kb-elmo/sesame/acrylic_case/sheet-frame-bottom-usb.dxf

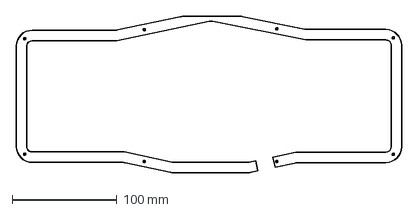
[picture p15: CAD file, 2021-01-16]
acrylic_case/sheet-frame-bottom-usb.dxf
368.4 x 149.6 mm
