kb-elmo/sesame/acrylic_case/sheet-frame-bottom.dxf

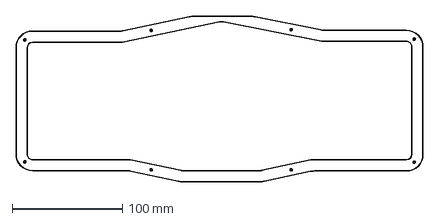
[picture p16: CAD file, 2021-01-16]
acrylic_case/sheet-frame-bottom.dxf
368.4 x 149.6 mm
