kb-elmo/sesame/acrylic_case/sheet-frame-top.dxf

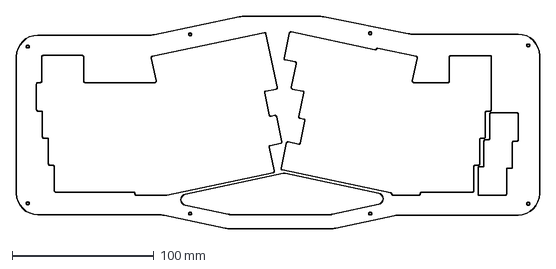
[picture p17: CAD file, 2021-01-16]
acrylic_case/sheet-frame-top.dxf
368.4 x 149.6 mm
