kb-elmo/sesame/acrylic_case/sheet-bottom.dxf

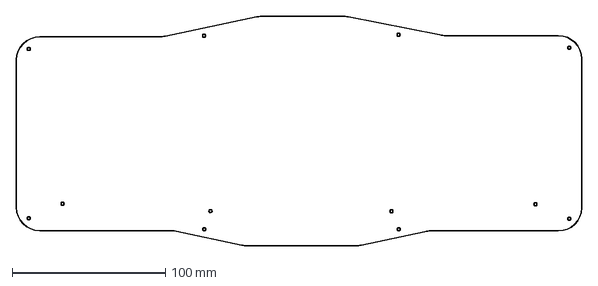
[picture p18: CAD file, 2021-01-16]
acrylic_case/sheet-bottom.dxf
368.4 x 149.6 mm
