kb-elmo/sesame/firmware/bootloader/updater/updater.asm

updater.elf:     file format elf32-avr

SYMBOL TABLE:
00000000 l    d  .text	00000000 .text
00800060 l    d  .data	00000000 .data
00000000 l    d  .comment	00000000 .comment
00000000 l    d  .note.gnu.avr.deviceinfo	00000000 .note.gnu.avr.deviceinfo
00000000 l    d  .debug_aranges	00000000 .debug_aranges
00000000 l    d  .debug_info	00000000 .debug_info
00000000 l    d  .debug_abbrev	00000000 .debug_abbrev
00000000 l    d  .debug_line	00000000 .debug_line
00000000 l    d  .debug_frame	00000000 .debug_frame
00000000 l    d  .debug_str	00000000 .debug_str
00000000 l    d  .debug_loc	00000000 .debug_loc
00000000 l    d  .debug_ranges	00000000 .debug_ranges
00000000 l    d  .debug_macro	00000000 .debug_macro
00000000 l    df *ABS*	00000000 updater.c
0000003e l       *ABS*	00000000 __SP_H__
0000003d l       *ABS*	00000000 __SP_L__
0000003f l       *ABS*	00000000 __SREG__
00000000 l       *ABS*	00000000 __tmp_reg__
00000001 l       *ABS*	00000000 __zero_reg__
0000009c l       .text	00000000 loop20
000000ca l       .text	00000000 loop48
00000000 l    df *ABS*	00000000 _exit.o
00000c1c l       .text	00000000 __stop_program
0000007a  w      .text	00000000 __vector_1
00800060 g     O .data	00000002 new_firmware
0000ffa0 g       *ABS*	00000000 __DATA_REGION_LENGTH__
0000007c g     F .text	0000002e do_spm
00000a62 g     F .text	00000012 memcpy_PF
00000054 g       .text	00000000 __trampolines_start
00000c1e g       .text	00000000 _etext
0000007a  w      .text	00000000 __vector_12
0000007a g       .text	00000000 __bad_interrupt
00000204 g       .text	00000000 usbasploader
00000c20 g       *ABS*	00000000 __data_load_end
0000007a  w      .text	00000000 __vector_6
00000054 g       .text	00000000 __trampolines_end
0000007a  w      .text	00000000 __vector_3
00000c1e g       *ABS*	00000000 __data_load_start
00000054 g       .text	00000000 __dtors_end
00000400 g       *ABS*	00000000 __LOCK_REGION_LENGTH__
0000007a  w      .text	00000000 __vector_11
00000054  w      .text	00000000 __init
00000a62 g       .text	00000000 _binary_usbasploader_raw_end
0000007a  w      .text	00000000 __vector_13
0000007a  w      .text	00000000 __vector_17
0000007a  w      .text	00000000 __vector_19
0000007a  w      .text	00000000 __vector_7
00810000 g       .data	00000000 __eeprom_end
00000000 g       .text	00000000 __vectors
00800062 g       .data	00000000 __data_end
0000085e g       *ABS*	00000000 _binary_usbasploader_raw_size
00000000  w      .text	00000000 __vector_default
0000007a  w      .text	00000000 __vector_5
000000fe g     F .text	00000106 mypgm_WRITEpage
000000d8 g     F .text	00000026 mypgm_readpage
00000400 g       *ABS*	00000000 __SIGNATURE_REGION_LENGTH__
00000054 g       .text	00000000 __ctors_start
00000060 g       .text	00000016 .hidden __do_copy_data
00000c0c g     F .text	0000000e memset
00000a74 g     F .text	00000198 main
0000007a  w      .text	00000000 __vector_4
00000000  w      *ABS*	00000000 __heap_end
0000007a  w      .text	00000000 __vector_9
0000007a  w      .text	00000000 __vector_2
00000400 g       *ABS*	00000000 __USER_SIGNATURE_REGION_LENGTH__
0000007a  w      .text	00000000 __vector_15
00000054 g       .text	00000000 __dtors_start
00000054 g       .text	00000000 __ctors_end
0000085f  w      *ABS*	00000000 __stack
00800062 g       .data	00000000 _edata
00800062 g       .data	00000000 _end
0000007a  w      .text	00000000 __vector_8
00000c1a  w      .text	00000000 .hidden exit
00010000 g       *ABS*	00000000 __EEPROM_REGION_LENGTH__
00000c1a g       .text	00000000 .hidden _exit
0000007a  w      .text	00000000 __vector_14
000000aa g     F .text	0000002e temp_do_spm
0000007a  w      .text	00000000 __vector_10
0000007a  w      .text	00000000 __vector_16
00800060 g       .data	00000000 __data_start
0000007a  w      .text	00000000 __vector_18
00000400 g       *ABS*	00000000 __FUSE_REGION_LENGTH__
00020000 g       *ABS*	00000000 __TEXT_REGION_LENGTH__
0000007a  w      .text	00000000 __vector_20



Disassembly of section .text:

00000000 <__vectors>:
   0:	29 c0       	rjmp	.+82     	; 0x54 <__ctors_end>
   2:	00 00       	nop
   4:	3a c0       	rjmp	.+116    	; 0x7a <__bad_interrupt>
   6:	00 00       	nop
   8:	38 c0       	rjmp	.+112    	; 0x7a <__bad_interrupt>
   a:	00 00       	nop
   c:	36 c0       	rjmp	.+108    	; 0x7a <__bad_interrupt>
   e:	00 00       	nop
  10:	34 c0       	rjmp	.+104    	; 0x7a <__bad_interrupt>
  12:	00 00       	nop
  14:	32 c0       	rjmp	.+100    	; 0x7a <__bad_interrupt>
  16:	00 00       	nop
  18:	30 c0       	rjmp	.+96     	; 0x7a <__bad_interrupt>
  1a:	00 00       	nop
  1c:	2e c0       	rjmp	.+92     	; 0x7a <__bad_interrupt>
  1e:	00 00       	nop
  20:	2c c0       	rjmp	.+88     	; 0x7a <__bad_interrupt>
  22:	00 00       	nop
  24:	2a c0       	rjmp	.+84     	; 0x7a <__bad_interrupt>
  26:	00 00       	nop
  28:	28 c0       	rjmp	.+80     	; 0x7a <__bad_interrupt>
  2a:	00 00       	nop
  2c:	26 c0       	rjmp	.+76     	; 0x7a <__bad_interrupt>
  2e:	00 00       	nop
  30:	24 c0       	rjmp	.+72     	; 0x7a <__bad_interrupt>
  32:	00 00       	nop
  34:	22 c0       	rjmp	.+68     	; 0x7a <__bad_interrupt>
  36:	00 00       	nop
  38:	20 c0       	rjmp	.+64     	; 0x7a <__bad_interrupt>
  3a:	00 00       	nop
  3c:	1e c0       	rjmp	.+60     	; 0x7a <__bad_interrupt>
  3e:	00 00       	nop
  40:	1c c0       	rjmp	.+56     	; 0x7a <__bad_interrupt>
  42:	00 00       	nop
  44:	1a c0       	rjmp	.+52     	; 0x7a <__bad_interrupt>
  46:	00 00       	nop
  48:	18 c0       	rjmp	.+48     	; 0x7a <__bad_interrupt>
  4a:	00 00       	nop
  4c:	16 c0       	rjmp	.+44     	; 0x7a <__bad_interrupt>
  4e:	00 00       	nop
  50:	14 c0       	rjmp	.+40     	; 0x7a <__bad_interrupt>
	...

00000054 <__ctors_end>:
  54:	11 24       	eor	r1, r1
  56:	1f be       	out	0x3f, r1	; 63
  58:	cf e5       	ldi	r28, 0x5F	; 95
  5a:	d8 e0       	ldi	r29, 0x08	; 8
  5c:	de bf       	out	0x3e, r29	; 62
  5e:	cd bf       	out	0x3d, r28	; 61

00000060 <__do_copy_data>:
  60:	10 e0       	ldi	r17, 0x00	; 0
  62:	a0 e6       	ldi	r26, 0x60	; 96
  64:	b0 e0       	ldi	r27, 0x00	; 0
  66:	ee e1       	ldi	r30, 0x1E	; 30
  68:	fc e0       	ldi	r31, 0x0C	; 12
  6a:	02 c0       	rjmp	.+4      	; 0x70 <__do_copy_data+0x10>
  6c:	05 90       	lpm	r0, Z+
  6e:	0d 92       	st	X+, r0
  70:	a2 36       	cpi	r26, 0x62	; 98
  72:	b1 07       	cpc	r27, r17
  74:	d9 f7       	brne	.-10     	; 0x6c <__do_copy_data+0xc>
  76:	fe d4       	rcall	.+2556   	; 0xa74 <main>
  78:	d0 c5       	rjmp	.+2976   	; 0xc1a <_exit>

0000007a <__bad_interrupt>:
  7a:	c2 cf       	rjmp	.-124    	; 0x0 <__vectors>

0000007c <do_spm>:
      );												\
  })
#endif

#if (!(defined(BOOTLOADER_ADDRESS))) || (defined(NEW_BOOTLOADER_ADDRESS))
void do_spm(const uint32_t flash_byteaddress, const uint8_t spmcrval, const uint16_t dataword) {
  7c:	bf 92       	push	r11
  7e:	cf 92       	push	r12
  80:	df 92       	push	r13
  82:	d9 01       	movw	r26, r18
    __do_spm_Ex(flash_byteaddress, spmcrval, dataword, funcaddr___bootloader__do_spm >> 1);
  84:	ea e2       	ldi	r30, 0x2A	; 42
  86:	f8 e3       	ldi	r31, 0x38	; 56
  88:	0f 92       	push	r0
  8a:	1f 92       	push	r1
  8c:	d7 2e       	mov	r13, r23
  8e:	c6 2e       	mov	r12, r22
  90:	b8 2e       	mov	r11, r24
  92:	24 2f       	mov	r18, r20
  94:	1b 2e       	mov	r1, r27
  96:	0a 2e       	mov	r0, r26
  98:	09 95       	icall
  9a:	21 31       	cpi	r18, 0x11	; 17

0000009c <loop20>:
  9c:	f9 f7       	brne	.-2      	; 0x9c <loop20>
  9e:	1f 90       	pop	r1
  a0:	0f 90       	pop	r0
}
  a2:	df 90       	pop	r13
  a4:	cf 90       	pop	r12
  a6:	bf 90       	pop	r11
  a8:	08 95       	ret

000000aa <temp_do_spm>:
void new_do_spm(const uint32_t flash_byteaddress, const uint8_t spmcrval, const uint16_t dataword) {
    __do_spm_Ex(flash_byteaddress, spmcrval, dataword, NEW_SPM_ADDRESS >> 1);
}
#endif

void temp_do_spm(const uint32_t flash_byteaddress, const uint8_t spmcrval, const uint16_t dataword) {
  aa:	bf 92       	push	r11
  ac:	cf 92       	push	r12
  ae:	df 92       	push	r13
  b0:	d9 01       	movw	r26, r18
    __do_spm_Ex(flash_byteaddress, spmcrval, dataword, TEMP_SPM_ADDRESS >> 1);
  b2:	ea e2       	ldi	r30, 0x2A	; 42
  b4:	ff e3       	ldi	r31, 0x3F	; 63
  b6:	0f 92       	push	r0
  b8:	1f 92       	push	r1
  ba:	d7 2e       	mov	r13, r23
  bc:	c6 2e       	mov	r12, r22
  be:	b8 2e       	mov	r11, r24
  c0:	24 2f       	mov	r18, r20
  c2:	1b 2e       	mov	r1, r27
  c4:	0a 2e       	mov	r0, r26
  c6:	09 95       	icall
  c8:	21 31       	cpi	r18, 0x11	; 17

000000ca <loop48>:
  ca:	f9 f7       	brne	.-2      	; 0xca <loop48>
  cc:	1f 90       	pop	r1
  ce:	0f 90       	pop	r0
}
  d0:	df 90       	pop	r13
  d2:	cf 90       	pop	r12
  d4:	bf 90       	pop	r11
  d6:	08 95       	ret

000000d8 <mypgm_readpage>:
  
  return result;
}
#else
// replace it somehow with "memcpy_PF" in order to save some ops...
size_t mypgm_readpage(const mypgm_addr_t byteaddress,const void* buffer, const size_t bufferbytesize) {
  d8:	cf 93       	push	r28
  da:	df 93       	push	r29
  dc:	fa 01       	movw	r30, r20
  de:	e9 01       	movw	r28, r18
  size_t	result		= (bufferbytesize < SPM_PAGESIZE)?bufferbytesize:SPM_PAGESIZE;
  e0:	21 38       	cpi	r18, 0x81	; 129
  e2:	31 05       	cpc	r19, r1
  e4:	10 f0       	brcs	.+4      	; 0xea <mypgm_readpage+0x12>
  e6:	c0 e8       	ldi	r28, 0x80	; 128
  e8:	d0 e0       	ldi	r29, 0x00	; 0
  mypgm_addr_t	pageaddr	= byteaddress - (byteaddress % SPM_PAGESIZE);
  ea:	ab 01       	movw	r20, r22
  ec:	bc 01       	movw	r22, r24
  ee:	40 78       	andi	r20, 0x80	; 128
  
  mymemcpy_PF((void*)buffer, (uint_farptr_t)pageaddr, result);
  f0:	9e 01       	movw	r18, r28
  f2:	cf 01       	movw	r24, r30
  f4:	b6 d4       	rcall	.+2412   	; 0xa62 <memcpy_PF>
  
  return result;
}
  f6:	ce 01       	movw	r24, r28
  f8:	df 91       	pop	r29
  fa:	cf 91       	pop	r28
  fc:	08 95       	ret

000000fe <mypgm_WRITEpage>:
#endif

#ifdef CONFIG_UPDATER_REDUCEWRITES
size_t mypgm_WRITEpage(const mypgm_addr_t byteaddress,const void* buffer, const size_t bufferbytesize, mypgm_spminterface spmfunc) {
  fe:	2f 92       	push	r2
 100:	3f 92       	push	r3
 102:	4f 92       	push	r4
 104:	5f 92       	push	r5
 106:	6f 92       	push	r6
 108:	7f 92       	push	r7
 10a:	8f 92       	push	r8
 10c:	9f 92       	push	r9
 10e:	af 92       	push	r10
 110:	bf 92       	push	r11
 112:	cf 92       	push	r12
 114:	df 92       	push	r13
 116:	ef 92       	push	r14
 118:	ff 92       	push	r15
 11a:	0f 93       	push	r16
 11c:	1f 93       	push	r17
 11e:	cf 93       	push	r28
 120:	df 93       	push	r29
 122:	48 01       	movw	r8, r16
  size_t	result		= (bufferbytesize < SPM_PAGESIZE)?bufferbytesize:SPM_PAGESIZE;
 124:	e9 01       	movw	r28, r18
 126:	21 38       	cpi	r18, 0x81	; 129
 128:	31 05       	cpc	r19, r1
 12a:	10 f0       	brcs	.+4      	; 0x130 <mypgm_WRITEpage+0x32>
 12c:	c0 e8       	ldi	r28, 0x80	; 128
 12e:	d0 e0       	ldi	r29, 0x00	; 0
  size_t	pagesize	= result >> 1;
 130:	1e 01       	movw	r2, r28
 132:	36 94       	lsr	r3
 134:	27 94       	ror	r2
  uint16_t	*pagedata	= (void*)buffer;
  mypgm_addr_t	pageaddr_bakup	= byteaddress - (byteaddress % SPM_PAGESIZE);
 136:	6b 01       	movw	r12, r22
 138:	7c 01       	movw	r14, r24
 13a:	20 e8       	ldi	r18, 0x80	; 128
 13c:	c2 22       	and	r12, r18
  uint8_t	changed=0, needs_erase=0;
  uint16_t	deeword;
  size_t	i;
  
  // just check, if page needs a rewrite or an erase...
  for (i=0;i<pagesize;i+=1) {
 13e:	8a 01       	movw	r16, r20
 140:	da 01       	movw	r26, r20
 142:	90 e0       	ldi	r25, 0x00	; 0
 144:	80 e0       	ldi	r24, 0x00	; 0
  uint8_t	changed=0, needs_erase=0;
 146:	60 e0       	ldi	r22, 0x00	; 0
 148:	70 e0       	ldi	r23, 0x00	; 0
  for (i=0;i<pagesize;i+=1) {
 14a:	82 15       	cp	r24, r2
 14c:	93 05       	cpc	r25, r3
 14e:	71 f5       	brne	.+92     	; 0x1ac <mypgm_WRITEpage+0xae>
    if ((~deeword) != 0) needs_erase=1;
      
    pageaddr+=2;
  }

  if (changed) {
 150:	77 23       	and	r23, r23
 152:	09 f4       	brne	.+2      	; 0x156 <mypgm_WRITEpage+0x58>
 154:	54 c0       	rjmp	.+168    	; 0x1fe <mypgm_WRITEpage+0x100>
    
    if (needs_erase) {
 156:	66 23       	and	r22, r22
 158:	39 f0       	breq	.+14     	; 0x168 <mypgm_WRITEpage+0x6a>
      //do a page-erase, ATTANTION: flash only can be erased a limited number of times !
      spmfunc(pageaddr_bakup, updater_pageerasecode, 0);
 15a:	30 e0       	ldi	r19, 0x00	; 0
 15c:	20 e0       	ldi	r18, 0x00	; 0
 15e:	43 e0       	ldi	r20, 0x03	; 3
 160:	c7 01       	movw	r24, r14
 162:	b6 01       	movw	r22, r12
 164:	f4 01       	movw	r30, r8
 166:	09 95       	icall
  uint8_t	changed=0, needs_erase=0;
 168:	26 01       	movw	r4, r12
 16a:	37 01       	movw	r6, r14
 16c:	b1 2c       	mov	r11, r1
 16e:	a1 2c       	mov	r10, r1
    
    // from now on, the page is assumed empty !! (hopefully our code is located somewhere else!)
    // now, fill the tempoary buffer
    // ATTANTION: see comment on "do_spm" !
    pageaddr	= pageaddr_bakup;
    for (i=0;i<pagesize;i+=1) {
 170:	a2 14       	cp	r10, r2
 172:	b3 04       	cpc	r11, r3
 174:	91 f5       	brne	.+100    	; 0x1da <mypgm_WRITEpage+0xdc>
      spmfunc(pageaddr, updater_pagefillcode, pagedata[i]);
      pageaddr+=2;
    }
    
    // so, now finally write the page to the FLASH
    spmfunc(pageaddr_bakup, updater_pagewritecode, 0);
 176:	30 e0       	ldi	r19, 0x00	; 0
 178:	20 e0       	ldi	r18, 0x00	; 0
 17a:	45 e0       	ldi	r20, 0x05	; 5
 17c:	c7 01       	movw	r24, r14
 17e:	b6 01       	movw	r22, r12
 180:	f4 01       	movw	r30, r8
 182:	09 95       	icall
    result = 0;
  }
  
  
  return result;
}
 184:	ce 01       	movw	r24, r28
 186:	df 91       	pop	r29
 188:	cf 91       	pop	r28
 18a:	1f 91       	pop	r17
 18c:	0f 91       	pop	r16
 18e:	ff 90       	pop	r15
 190:	ef 90       	pop	r14
 192:	df 90       	pop	r13
 194:	cf 90       	pop	r12
 196:	bf 90       	pop	r11
 198:	af 90       	pop	r10
 19a:	9f 90       	pop	r9
 19c:	8f 90       	pop	r8
 19e:	7f 90       	pop	r7
 1a0:	6f 90       	pop	r6
 1a2:	5f 90       	pop	r5
 1a4:	4f 90       	pop	r4
 1a6:	3f 90       	pop	r3
 1a8:	2f 90       	pop	r2
 1aa:	08 95       	ret
    deeword=pgm_read_word(pageaddr);
 1ac:	fc 01       	movw	r30, r24
 1ae:	ee 0f       	add	r30, r30
 1b0:	ff 1f       	adc	r31, r31
 1b2:	ec 0d       	add	r30, r12
 1b4:	fd 1d       	adc	r31, r13
 1b6:	25 91       	lpm	r18, Z+
 1b8:	34 91       	lpm	r19, Z
    if (deeword != pagedata[i]) changed=1;
 1ba:	4d 91       	ld	r20, X+
 1bc:	5d 91       	ld	r21, X+
 1be:	42 17       	cp	r20, r18
 1c0:	53 07       	cpc	r21, r19
 1c2:	49 f0       	breq	.+18     	; 0x1d6 <mypgm_WRITEpage+0xd8>
    deeword |= ~pagedata[i];
 1c4:	40 95       	com	r20
 1c6:	50 95       	com	r21
 1c8:	24 2b       	or	r18, r20
 1ca:	35 2b       	or	r19, r21
    if (deeword != pagedata[i]) changed=1;
 1cc:	71 e0       	ldi	r23, 0x01	; 1
    if ((~deeword) != 0) needs_erase=1;
 1ce:	2f 3f       	cpi	r18, 0xFF	; 255
 1d0:	3f 4f       	sbci	r19, 0xFF	; 255
 1d2:	09 f0       	breq	.+2      	; 0x1d6 <mypgm_WRITEpage+0xd8>
 1d4:	61 e0       	ldi	r22, 0x01	; 1
  for (i=0;i<pagesize;i+=1) {
 1d6:	01 96       	adiw	r24, 0x01	; 1
 1d8:	b8 cf       	rjmp	.-144    	; 0x14a <mypgm_WRITEpage+0x4c>
      spmfunc(pageaddr, updater_pagefillcode, pagedata[i]);
 1da:	f8 01       	movw	r30, r16
 1dc:	21 91       	ld	r18, Z+
 1de:	31 91       	ld	r19, Z+
 1e0:	8f 01       	movw	r16, r30
 1e2:	41 e0       	ldi	r20, 0x01	; 1
 1e4:	c3 01       	movw	r24, r6
 1e6:	b2 01       	movw	r22, r4
 1e8:	f4 01       	movw	r30, r8
 1ea:	09 95       	icall
      pageaddr+=2;
 1ec:	f2 e0       	ldi	r31, 0x02	; 2
 1ee:	4f 0e       	add	r4, r31
 1f0:	51 1c       	adc	r5, r1
 1f2:	61 1c       	adc	r6, r1
 1f4:	71 1c       	adc	r7, r1
    for (i=0;i<pagesize;i+=1) {
 1f6:	2f ef       	ldi	r18, 0xFF	; 255
 1f8:	a2 1a       	sub	r10, r18
 1fa:	b2 0a       	sbc	r11, r18
 1fc:	b9 cf       	rjmp	.-142    	; 0x170 <mypgm_WRITEpage+0x72>
    result = 0;
 1fe:	d0 e0       	ldi	r29, 0x00	; 0
 200:	c0 e0       	ldi	r28, 0x00	; 0
  return result;
 202:	c0 cf       	rjmp	.-128    	; 0x184 <mypgm_WRITEpage+0x86>

00000204 <usbasploader>:
 204:	61 c0       	rjmp	.+194    	; 0x2c8 <usbasploader+0xc4>
 206:	00 00       	nop
 208:	a0 c0       	rjmp	.+320    	; 0x34a <usbasploader+0x146>
 20a:	00 00       	nop
 20c:	84 c0       	rjmp	.+264    	; 0x316 <usbasploader+0x112>
 20e:	00 00       	nop
 210:	82 c0       	rjmp	.+260    	; 0x316 <usbasploader+0x112>
 212:	00 00       	nop
 214:	80 c0       	rjmp	.+256    	; 0x316 <usbasploader+0x112>
 216:	00 00       	nop
 218:	7e c0       	rjmp	.+252    	; 0x316 <usbasploader+0x112>
 21a:	00 00       	nop
 21c:	7c c0       	rjmp	.+248    	; 0x316 <usbasploader+0x112>
 21e:	00 00       	nop
 220:	7a c0       	rjmp	.+244    	; 0x316 <usbasploader+0x112>
 222:	00 00       	nop
 224:	78 c0       	rjmp	.+240    	; 0x316 <usbasploader+0x112>
 226:	00 00       	nop
 228:	76 c0       	rjmp	.+236    	; 0x316 <usbasploader+0x112>
 22a:	00 00       	nop
 22c:	74 c0       	rjmp	.+232    	; 0x316 <usbasploader+0x112>
 22e:	00 00       	nop
 230:	72 c0       	rjmp	.+228    	; 0x316 <usbasploader+0x112>
 232:	00 00       	nop
 234:	70 c0       	rjmp	.+224    	; 0x316 <usbasploader+0x112>
 236:	00 00       	nop
 238:	6e c0       	rjmp	.+220    	; 0x316 <usbasploader+0x112>
 23a:	00 00       	nop
 23c:	6c c0       	rjmp	.+216    	; 0x316 <usbasploader+0x112>
 23e:	00 00       	nop
 240:	6a c0       	rjmp	.+212    	; 0x316 <usbasploader+0x112>
 242:	00 00       	nop
 244:	68 c0       	rjmp	.+208    	; 0x316 <usbasploader+0x112>
 246:	00 00       	nop
 248:	66 c0       	rjmp	.+204    	; 0x316 <usbasploader+0x112>
 24a:	00 00       	nop
 24c:	64 c0       	rjmp	.+200    	; 0x316 <usbasploader+0x112>
 24e:	00 00       	nop
 250:	62 c0       	rjmp	.+196    	; 0x316 <usbasploader+0x112>
 252:	00 00       	nop
 254:	60 c0       	rjmp	.+192    	; 0x316 <usbasploader+0x112>
 256:	00 00       	nop
 258:	ec 2d       	mov	r30, r12
 25a:	fd 2d       	mov	r31, r13
 25c:	b7 b6       	in	r11, 0x37	; 55
 25e:	b0 fc       	sbrc	r11, 0
 260:	fd cf       	rjmp	.-6      	; 0x25c <usbasploader+0x58>
 262:	27 bf       	out	0x37, r18	; 55
 264:	e8 95       	spm
 266:	b7 b6       	in	r11, 0x37	; 55
 268:	b0 fc       	sbrc	r11, 0
 26a:	fd cf       	rjmp	.-6      	; 0x266 <usbasploader+0x62>
 26c:	21 e1       	ldi	r18, 0x11	; 17
 26e:	b7 b6       	in	r11, 0x37	; 55
 270:	b6 fc       	sbrc	r11, 6
 272:	f4 cf       	rjmp	.-24     	; 0x25c <usbasploader+0x58>
 274:	08 95       	ret
 276:	09 02       	muls	r16, r25
 278:	12 00       	.word	0x0012	; ????
 27a:	01 01       	movw	r0, r2
 27c:	00 80       	ld	r0, Z
 27e:	32 09       	sbc	r19, r2
 280:	04 00       	.word	0x0004	; ????
 282:	00 00       	nop
 284:	00 00       	nop
 286:	00 00       	nop
 288:	12 01       	movw	r2, r4
 28a:	10 01       	movw	r2, r0
 28c:	ff 00       	.word	0x00ff	; ????
 28e:	00 08       	sbc	r0, r0
 290:	c0 16       	cp	r12, r16
 292:	dc 05       	cpc	r29, r12
 294:	02 01       	movw	r0, r4
 296:	01 02       	muls	r16, r17
 298:	00 01       	movw	r0, r0
 29a:	0e 03       	fmul	r16, r22
 29c:	55 00       	.word	0x0055	; ????
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
 a52:	0f be       	out	0x3f, r0	; 63
 a54:	01 96       	adiw	r24, 0x01	; 1
 a56:	08 95       	ret
 a58:	f8 94       	cli
 a5a:	ff cf       	rjmp	.-2      	; 0xa5a <__stack+0x1fb>
 a5c:	ff 5a       	subi	r31, 0xAF	; 175
 a5e:	1e 95 02 00 	call	0x440004	; 0x440004 <__TEXT_REGION_LENGTH__+0x420004>

00000a62 <memcpy_PF>:
 a62:	fa 01       	movw	r30, r20
 a64:	dc 01       	movw	r26, r24
 a66:	02 c0       	rjmp	.+4      	; 0xa6c <memcpy_PF+0xa>
 a68:	05 90       	lpm	r0, Z+
 a6a:	0d 92       	st	X+, r0
 a6c:	21 50       	subi	r18, 0x01	; 1
 a6e:	30 40       	sbci	r19, 0x00	; 0
 a70:	d8 f7       	brcc	.-10     	; 0xa68 <memcpy_PF+0x6>
 a72:	08 95       	ret

00000a74 <main>:
#include "crccheck.c"
#endif

// #pragma GCC diagnostic ignored "-Wno-pointer-to-int-cast"
int main(void)
{
 a74:	cd b7       	in	r28, 0x3d	; 61
 a76:	de b7       	in	r29, 0x3e	; 62
 a78:	c0 58       	subi	r28, 0x80	; 128
 a7a:	d1 09       	sbc	r29, r1
 a7c:	0f b6       	in	r0, 0x3f	; 63
 a7e:	f8 94       	cli
 a80:	de bf       	out	0x3e, r29	; 62
 a82:	0f be       	out	0x3f, r0	; 63
 a84:	cd bf       	out	0x3d, r28	; 61
    uint32_t crcval;
#endif
    size_t  i;
    uint8_t buffer[SPM_PAGESIZE];
    
    MCUCSR = 0; /* do not care about previous reset - just disable the wdt */
 a86:	14 be       	out	0x34, r1	; 52
void wdt_disable (void)
{
	if (_SFR_IO_REG_P (_WD_CONTROL_REG))
	{
        uint8_t register temp_reg;
		__asm__ __volatile__ (
 a88:	0f b6       	in	r0, 0x3f	; 63
 a8a:	f8 94       	cli
 a8c:	a8 95       	wdr
 a8e:	81 b5       	in	r24, 0x21	; 33
 a90:	88 61       	ori	r24, 0x18	; 24
 a92:	81 bd       	out	0x21, r24	; 33
 a94:	11 bc       	out	0x21, r1	; 33
 a96:	0f be       	out	0x3f, r0	; 63
    wdt_disable();
    cli();
 a98:	f8 94       	cli
    if (crcval == ((uint32_t)UPDATECRC32)) {
#endif

    // check if firmware would change...
    buffer[0]=0;
    for (i=0;i<SIZEOF_new_firmware;i+=2) {
 a9a:	20 91 60 00 	lds	r18, 0x0060	; 0x800060 <new_firmware>
 a9e:	30 91 61 00 	lds	r19, 0x0061	; 0x800061 <new_firmware+0x1>
      uint16_t a, b;
#if (FLASHEND > 65535)
      a=pgm_read_word_far(FULLCORRECTFLASHADDRESS(&new_firmware[i]));
      b=pgm_read_word_far(NEW_BOOTLOADER_ADDRESS+i);
#else
      a=pgm_read_word(FULLCORRECTFLASHADDRESS(&new_firmware[i]));
 aa2:	80 e0       	ldi	r24, 0x00	; 0
 aa4:	90 e7       	ldi	r25, 0x70	; 112
 aa6:	f9 01       	movw	r30, r18
 aa8:	65 91       	lpm	r22, Z+
 aaa:	74 91       	lpm	r23, Z
      b=pgm_read_word(NEW_BOOTLOADER_ADDRESS+i);
 aac:	fc 01       	movw	r30, r24
 aae:	45 91       	lpm	r20, Z+
 ab0:	54 91       	lpm	r21, Z
#endif
      if (a!=b) {
 ab2:	64 17       	cp	r22, r20
 ab4:	75 07       	cpc	r23, r21
 ab6:	09 f4       	brne	.+2      	; 0xaba <main+0x46>
 ab8:	94 c0       	rjmp	.+296    	; 0xbe2 <main+0x16e>
	buffer[0]=1;
 aba:	81 e0       	ldi	r24, 0x01	; 1
 abc:	89 83       	std	Y+1, r24	; 0x01
 abe:	94 e5       	ldi	r25, 0x54	; 84
 ac0:	c9 2e       	mov	r12, r25
 ac2:	90 e7       	ldi	r25, 0x70	; 112
 ac4:	d9 2e       	mov	r13, r25
 ac6:	e1 2c       	mov	r14, r1
 ac8:	f1 2c       	mov	r15, r1
  mypgm_addr_t	pageaddr	= byteaddress - (byteaddress % SPM_PAGESIZE);
 aca:	b7 01       	movw	r22, r14
 acc:	a6 01       	movw	r20, r12
 ace:	40 78       	andi	r20, 0x80	; 128
  mymemcpy_PF((void*)buffer, (uint_farptr_t)pageaddr, result);
 ad0:	20 e8       	ldi	r18, 0x80	; 128
 ad2:	30 e0       	ldi	r19, 0x00	; 0
 ad4:	ce 01       	movw	r24, r28
 ad6:	01 96       	adiw	r24, 0x01	; 1
 ad8:	c4 df       	rcall	.-120    	; 0xa62 <memcpy_PF>
    if (buffer[0]) {

      // A
      // copy the current "bootloader__do_spm" to tempoary position via std. "bootloader__do_spm"
      for (i=0;i<TEMP_SPM_BLKSIZE;i+=SPM_PAGESIZE) {
	mypgm_WRITEpage(TEMP_SPM_PAGEADR+i, buffer, mypgm_readpage(funcaddr___bootloader__do_spm+i, buffer, sizeof(buffer)), do_spm);
 ada:	c7 01       	movw	r24, r14
 adc:	b6 01       	movw	r22, r12
 ade:	64 55       	subi	r22, 0x54	; 84
 ae0:	72 4f       	sbci	r23, 0xF2	; 242
 ae2:	8f 4f       	sbci	r24, 0xFF	; 255
 ae4:	9f 4f       	sbci	r25, 0xFF	; 255
 ae6:	0e e3       	ldi	r16, 0x3E	; 62
 ae8:	10 e0       	ldi	r17, 0x00	; 0
 aea:	20 e8       	ldi	r18, 0x80	; 128
 aec:	30 e0       	ldi	r19, 0x00	; 0
 aee:	ae 01       	movw	r20, r28
 af0:	4f 5f       	subi	r20, 0xFF	; 255
 af2:	5f 4f       	sbci	r21, 0xFF	; 255
 af4:	04 db       	rcall	.-2552   	; 0xfe <mypgm_WRITEpage>
 af6:	80 e8       	ldi	r24, 0x80	; 128
 af8:	c8 0e       	add	r12, r24
 afa:	d1 1c       	adc	r13, r1
 afc:	e1 1c       	adc	r14, r1
 afe:	f1 1c       	adc	r15, r1
      for (i=0;i<TEMP_SPM_BLKSIZE;i+=SPM_PAGESIZE) {
 b00:	24 e5       	ldi	r18, 0x54	; 84
 b02:	c2 16       	cp	r12, r18
 b04:	22 e7       	ldi	r18, 0x72	; 114
 b06:	d2 06       	cpc	r13, r18
 b08:	e1 04       	cpc	r14, r1
 b0a:	f1 04       	cpc	r15, r1
 b0c:	f1 f6       	brne	.-68     	; 0xaca <main+0x56>
 b0e:	c1 2c       	mov	r12, r1
 b10:	80 e7       	ldi	r24, 0x70	; 112
 b12:	d8 2e       	mov	r13, r24
 b14:	e1 2c       	mov	r14, r1
 b16:	f1 2c       	mov	r15, r1
 b18:	56 01       	movw	r10, r12
 b1a:	40 e7       	ldi	r20, 0x70	; 112
 b1c:	b4 1a       	sub	r11, r20
      // B
      // start updating the firmware to "NEW_BOOTLOADER_ADDRESS" until at least "TEMP_SPM_BLKSIZE"-bytes after "NEW_SPM_ADDRESS" were written
      // therefore use the tempoary "bootloader__do_spm" (since we most probably will overwrite the default do_spm)
      for (i=0;;i+=SPM_PAGESIZE) {
#ifdef CONFIG_UPDATER_CLEANMEMCLEAR
	memset((void*)buffer, 0xff, sizeof(buffer));
 b1e:	40 e8       	ldi	r20, 0x80	; 128
 b20:	50 e0       	ldi	r21, 0x00	; 0
 b22:	6f ef       	ldi	r22, 0xFF	; 255
 b24:	70 e0       	ldi	r23, 0x00	; 0
 b26:	ce 01       	movw	r24, r28
 b28:	01 96       	adiw	r24, 0x01	; 1
 b2a:	70 d0       	rcall	.+224    	; 0xc0c <memset>
#endif
	mymemcpy_PF((void*)buffer, (uint_farptr_t)(FULLCORRECTFLASHADDRESS(&new_firmware[i])), ((SIZEOF_new_firmware-i)>sizeof(buffer))?sizeof(buffer):(SIZEOF_new_firmware-i));
 b2c:	40 91 60 00 	lds	r20, 0x0060	; 0x800060 <new_firmware>
 b30:	50 91 61 00 	lds	r21, 0x0061	; 0x800061 <new_firmware+0x1>
 b34:	4a 0d       	add	r20, r10
 b36:	5b 1d       	adc	r21, r11
 b38:	05 2e       	mov	r0, r21
 b3a:	00 0c       	add	r0, r0
 b3c:	66 0b       	sbc	r22, r22
 b3e:	77 0b       	sbc	r23, r23
 b40:	20 e8       	ldi	r18, 0x80	; 128
 b42:	30 e0       	ldi	r19, 0x00	; 0
 b44:	ce 01       	movw	r24, r28
 b46:	01 96       	adiw	r24, 0x01	; 1
 b48:	8c df       	rcall	.-232    	; 0xa62 <memcpy_PF>
	
	mypgm_WRITEpage(NEW_BOOTLOADER_ADDRESS+i, buffer, sizeof(buffer), temp_do_spm);
 b4a:	05 e5       	ldi	r16, 0x55	; 85
 b4c:	10 e0       	ldi	r17, 0x00	; 0
 b4e:	20 e8       	ldi	r18, 0x80	; 128
 b50:	30 e0       	ldi	r19, 0x00	; 0
 b52:	ae 01       	movw	r20, r28
 b54:	4f 5f       	subi	r20, 0xFF	; 255
 b56:	5f 4f       	sbci	r21, 0xFF	; 255
 b58:	c7 01       	movw	r24, r14
 b5a:	b6 01       	movw	r22, r12
 b5c:	d0 da       	rcall	.-2656   	; 0xfe <mypgm_WRITEpage>
	
	if ((NEW_BOOTLOADER_ADDRESS+i) > (NEW_SPM_ADDRESS+TEMP_SPM_BLKSIZE)) break;
 b5e:	d7 01       	movw	r26, r14
 b60:	c6 01       	movw	r24, r12
 b62:	80 58       	subi	r24, 0x80	; 128
 b64:	9f 4f       	sbci	r25, 0xFF	; 255
 b66:	af 4f       	sbci	r26, 0xFF	; 255
 b68:	bf 4f       	sbci	r27, 0xFF	; 255
 b6a:	81 15       	cp	r24, r1
 b6c:	23 e7       	ldi	r18, 0x73	; 115
 b6e:	92 07       	cpc	r25, r18
 b70:	a1 05       	cpc	r26, r1
 b72:	b1 05       	cpc	r27, r1
 b74:	09 f0       	breq	.+2      	; 0xb78 <main+0x104>
 b76:	47 c0       	rjmp	.+142    	; 0xc06 <main+0x192>

      // C
      // continue writeing the new_firmware after "NEW_SPM_ADDRESS+TEMP_SPM_BLKSIZE" this time use the "new_do_spm"
      for (;i<SIZEOF_new_firmware;i+=SPM_PAGESIZE) {
#ifdef CONFIG_UPDATER_CLEANMEMCLEAR
	memset((void*)buffer, 0xff, sizeof(buffer));
 b78:	40 e8       	ldi	r20, 0x80	; 128
 b7a:	50 e0       	ldi	r21, 0x00	; 0
 b7c:	6f ef       	ldi	r22, 0xFF	; 255
 b7e:	70 e0       	ldi	r23, 0x00	; 0
 b80:	ce 01       	movw	r24, r28
 b82:	01 96       	adiw	r24, 0x01	; 1
 b84:	43 d0       	rcall	.+134    	; 0xc0c <memset>
#endif
	mymemcpy_PF((void*)buffer, (uint_farptr_t)(FULLCORRECTFLASHADDRESS(&new_firmware[i])), ((SIZEOF_new_firmware-i)>sizeof(buffer))?sizeof(buffer):(SIZEOF_new_firmware-i));
 b86:	2e e5       	ldi	r18, 0x5E	; 94
 b88:	38 e0       	ldi	r19, 0x08	; 8
 b8a:	2a 19       	sub	r18, r10
 b8c:	3b 09       	sbc	r19, r11
 b8e:	21 38       	cpi	r18, 0x81	; 129
 b90:	31 05       	cpc	r19, r1
 b92:	10 f0       	brcs	.+4      	; 0xb98 <main+0x124>
 b94:	20 e8       	ldi	r18, 0x80	; 128
 b96:	30 e0       	ldi	r19, 0x00	; 0
 b98:	40 91 60 00 	lds	r20, 0x0060	; 0x800060 <new_firmware>
 b9c:	50 91 61 00 	lds	r21, 0x0061	; 0x800061 <new_firmware+0x1>
 ba0:	4a 0d       	add	r20, r10
 ba2:	5b 1d       	adc	r21, r11
 ba4:	05 2e       	mov	r0, r21
 ba6:	00 0c       	add	r0, r0
 ba8:	66 0b       	sbc	r22, r22
 baa:	77 0b       	sbc	r23, r23
 bac:	ce 01       	movw	r24, r28
 bae:	01 96       	adiw	r24, 0x01	; 1
 bb0:	58 df       	rcall	.-336    	; 0xa62 <memcpy_PF>

	mypgm_WRITEpage(NEW_BOOTLOADER_ADDRESS+i, buffer, sizeof(buffer), new_do_spm);
 bb2:	0e e3       	ldi	r16, 0x3E	; 62
 bb4:	10 e0       	ldi	r17, 0x00	; 0
 bb6:	20 e8       	ldi	r18, 0x80	; 128
 bb8:	30 e0       	ldi	r19, 0x00	; 0
 bba:	ae 01       	movw	r20, r28
 bbc:	4f 5f       	subi	r20, 0xFF	; 255
 bbe:	5f 4f       	sbci	r21, 0xFF	; 255
 bc0:	c7 01       	movw	r24, r14
 bc2:	b6 01       	movw	r22, r12
 bc4:	9c da       	rcall	.-2760   	; 0xfe <mypgm_WRITEpage>
      for (;i<SIZEOF_new_firmware;i+=SPM_PAGESIZE) {
 bc6:	40 e8       	ldi	r20, 0x80	; 128
 bc8:	a4 0e       	add	r10, r20
 bca:	b1 1c       	adc	r11, r1
 bcc:	80 e8       	ldi	r24, 0x80	; 128
 bce:	c8 0e       	add	r12, r24
 bd0:	d1 1c       	adc	r13, r1
 bd2:	e1 1c       	adc	r14, r1
 bd4:	f1 1c       	adc	r15, r1
 bd6:	2e e5       	ldi	r18, 0x5E	; 94
 bd8:	a2 16       	cp	r10, r18
 bda:	28 e0       	ldi	r18, 0x08	; 8
 bdc:	b2 06       	cpc	r11, r18
 bde:	60 f2       	brcs	.-104    	; 0xb78 <main+0x104>
 be0:	08 c0       	rjmp	.+16     	; 0xbf2 <main+0x17e>
 be2:	2e 5f       	subi	r18, 0xFE	; 254
 be4:	3f 4f       	sbci	r19, 0xFF	; 255
 be6:	02 96       	adiw	r24, 0x02	; 2
    for (i=0;i<SIZEOF_new_firmware;i+=2) {
 be8:	8e 35       	cpi	r24, 0x5E	; 94
 bea:	48 e7       	ldi	r20, 0x78	; 120
 bec:	94 07       	cpc	r25, r20
 bee:	09 f0       	breq	.+2      	; 0xbf2 <main+0x17e>
 bf0:	5a cf       	rjmp	.-332    	; 0xaa6 <main+0x32>
#if defined(UPDATECRC32)
    }
#endif

    return 0;
}
 bf2:	90 e0       	ldi	r25, 0x00	; 0
 bf4:	80 e0       	ldi	r24, 0x00	; 0
 bf6:	c0 58       	subi	r28, 0x80	; 128
 bf8:	df 4f       	sbci	r29, 0xFF	; 255
 bfa:	0f b6       	in	r0, 0x3f	; 63
 bfc:	f8 94       	cli
 bfe:	de bf       	out	0x3e, r29	; 62
 c00:	0f be       	out	0x3f, r0	; 63
 c02:	cd bf       	out	0x3d, r28	; 61
 c04:	08 95       	ret
 c06:	6c 01       	movw	r12, r24
 c08:	7d 01       	movw	r14, r26
 c0a:	86 cf       	rjmp	.-244    	; 0xb18 <main+0xa4>

00000c0c <memset>:
 c0c:	dc 01       	movw	r26, r24
 c0e:	01 c0       	rjmp	.+2      	; 0xc12 <memset+0x6>
 c10:	6d 93       	st	X+, r22
 c12:	41 50       	subi	r20, 0x01	; 1
 c14:	50 40       	sbci	r21, 0x00	; 0
 c16:	e0 f7       	brcc	.-8      	; 0xc10 <memset+0x4>
 c18:	08 95       	ret

00000c1a <_exit>:
 c1a:	f8 94       	cli

00000c1c <__stop_program>:
 c1c:	ff cf       	rjmp	.-2      	; 0xc1c <__stop_program>
